Javierma/lightwand-texas-edition/eagle project/Lightwand_USB_power/LightWand_USB_power.dxf

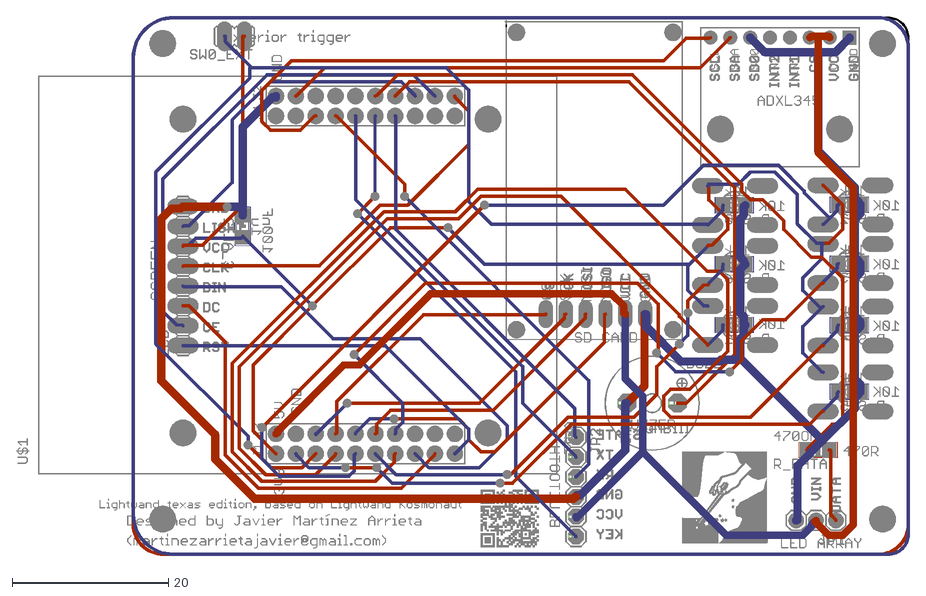
[picture p43: CAD file, 2018-04-30]
eagle project/Lightwand_USB_power/LightWand_USB_power.dxf
114.2 x 69.0
